Darkone83/Type-D/images/Board prep/S3_PWR_EN.JPG

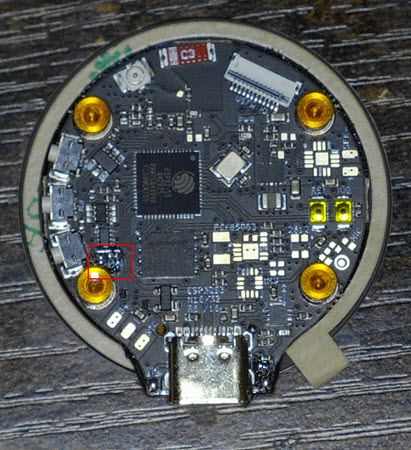
images/Board prep/S3_PWR_EN.JPG
