Darkone83/Type-D/FATFS Setup/boot/boot.gif

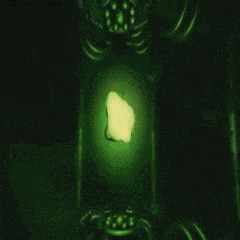
FATFS Setup/boot/boot.gif
