Darkone83/Type-D/FATFS Setup/gif/anime.gif

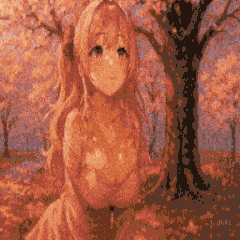
FATFS Setup/gif/anime.gif
