Darkone83/Type-D/FATFS Setup/gif/conker.gif

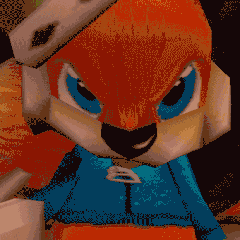
FATFS Setup/gif/conker.gif
