Darkone83/Type-D/FATFS Setup/gif/halo.gif

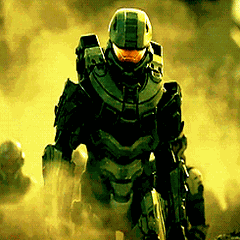
FATFS Setup/gif/halo.gif
