Darkone83/Type-D/FATFS Setup/jpg/mc.jpg

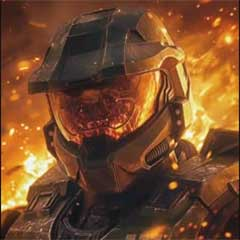
FATFS Setup/jpg/mc.jpg
