Darkone83/Type-D/FATFS Setup/jpg/xbox.jpg

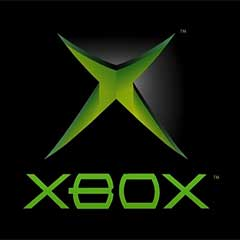
FATFS Setup/jpg/xbox.jpg
