Darkone83/Type-D/src/ui_bright.h

#ifndef UI_BRIGHT_H
#define UI_BRIGHT_H

#include <Arduino.h>
#include "CST816S.h"

void ui_bright_open();   // Call this with your touch pointer
void ui_bright_exit();
bool ui_bright_isVisible();
void ui_bright_update();
void ui_bright_applySaved();

#endif // UI_BRIGHT_H
